wenbang24/idiot12-wireless/img/renderv1_6.png

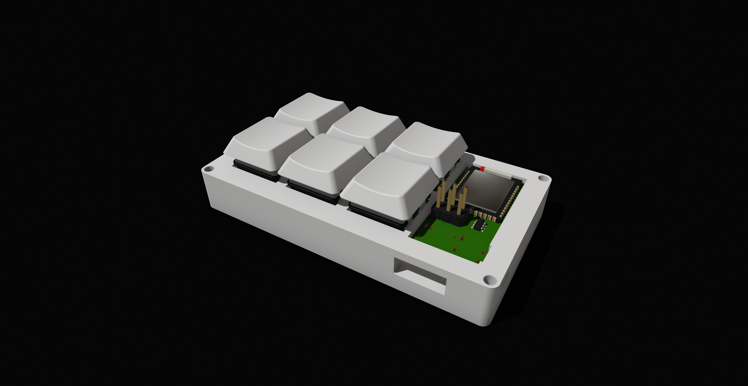
img/renderv1_6.png
